Kapkupi/RPI5-Palmtop/CAD/SolidWorks/heatsink/raspberry-pi-5-2.snapshot.8/Photo/iWcUdrz5w2npCPwYrjM4Qg-970-80.jpg

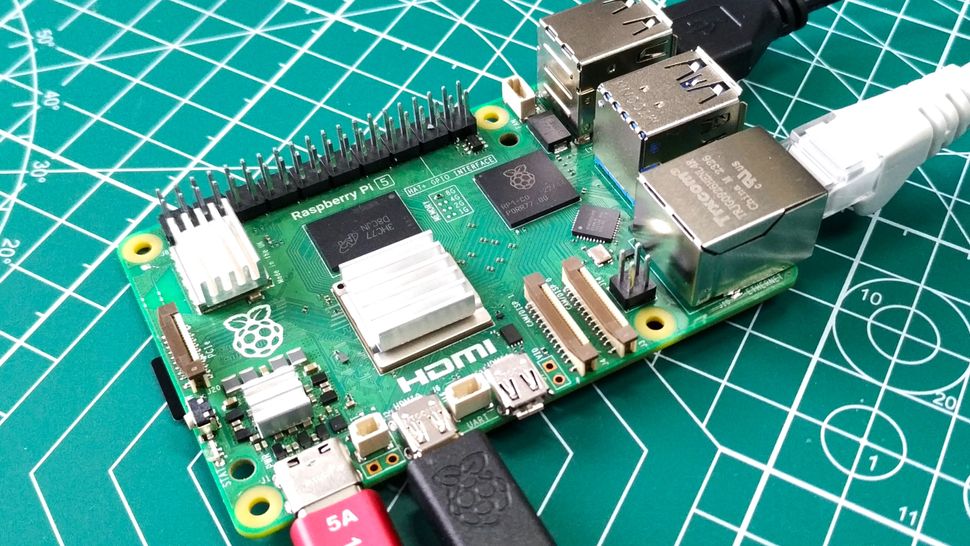
CAD/SolidWorks/heatsink/raspberry-pi-5-2.snapshot.8/Photo/iWcUdrz5w2npCPwYrjM4Qg-970-80.jpg
