Kapkupi/RPI5-Palmtop/CAD/SolidWorks/heatsink/raspberry-pi-5-2.snapshot.8/Photo/raspberry pi 5.png

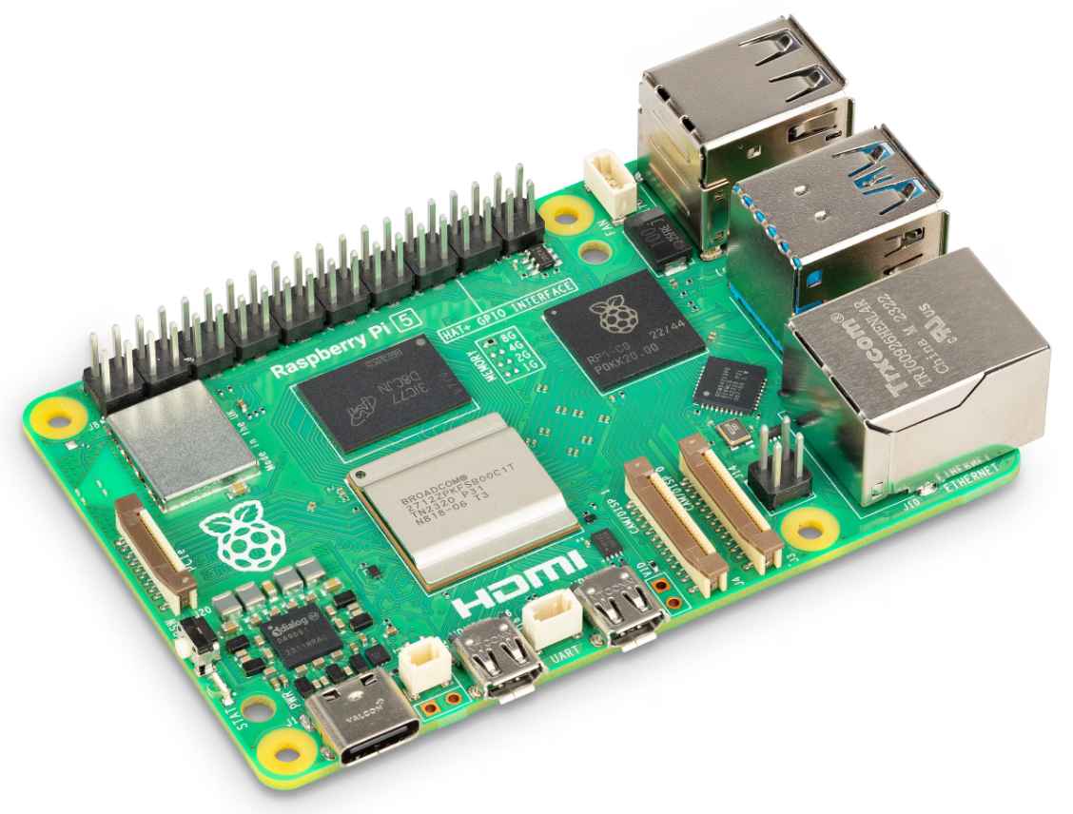
CAD/SolidWorks/heatsink/raspberry-pi-5-2.snapshot.8/Photo/raspberry pi 5.png
