Kapkupi/RPI5-Palmtop/CAD/SolidWorks/heatsink/raspberry-pi-5-2.snapshot.8/RENDERS/Raspberry Pi (2)_Ładny wygląd.png

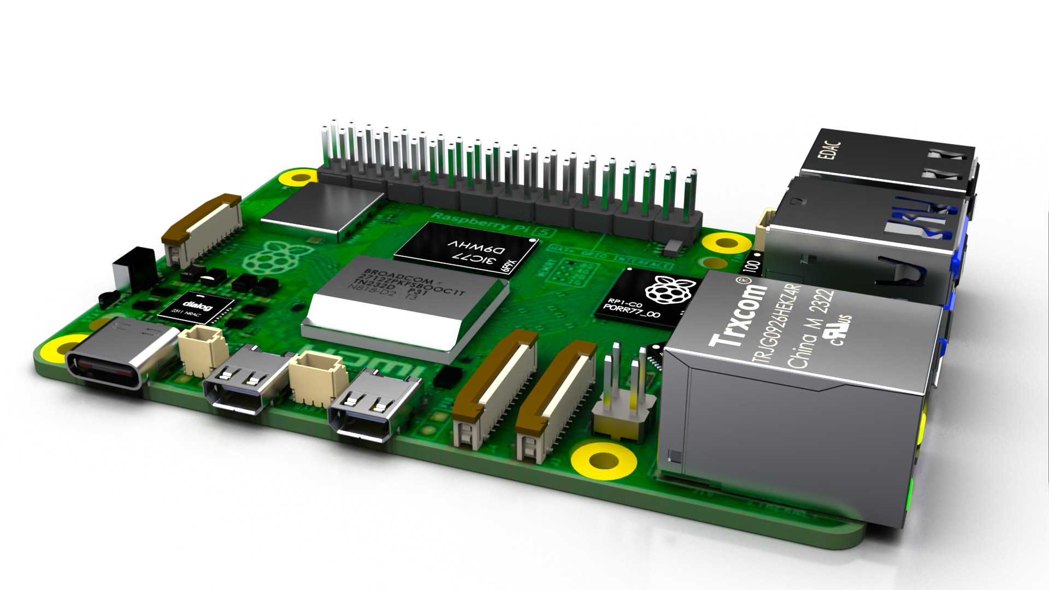
CAD/SolidWorks/heatsink/raspberry-pi-5-2.snapshot.8/RENDERS/Raspberry Pi (2)_Ładny wygląd.png
