Kapkupi/RPI5-Palmtop/CAD/SolidWorks/heatsink/raspberry-pi-5-2.snapshot.8/RENDERS/RASPBERRY_PI_5_1.png

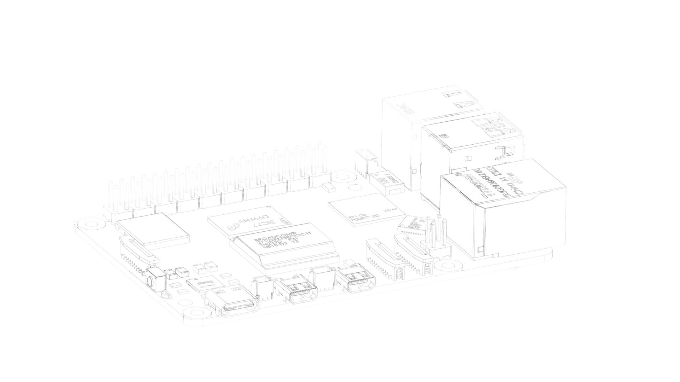
CAD/SolidWorks/heatsink/raspberry-pi-5-2.snapshot.8/RENDERS/RASPBERRY_PI_5_1.png
