Kapkupi/RPI5-Palmtop/step/face_plate.STEP

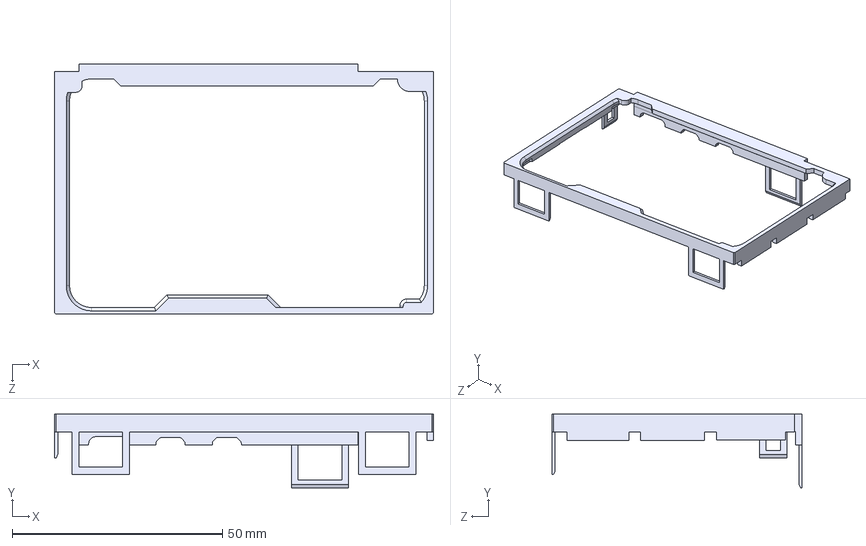
[picture p26: CAD file, 2026-09-20]
step/face_plate.STEP
90.2 x 17.5 x 59.6 mm
