Kapkupi/RPI5-Palmtop/CAD/SolidWorks/heatsink/display_button.SLDPRT

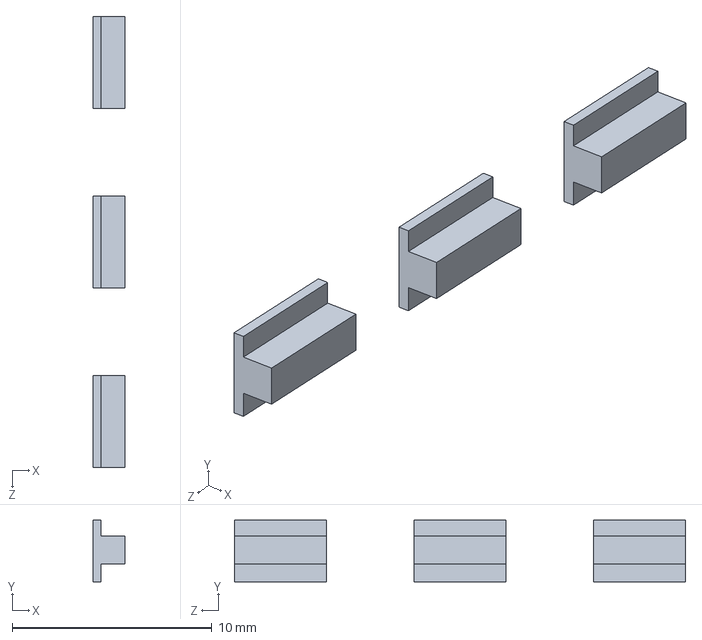
[picture p27: CAD file, 2026-09-20]
CAD/SolidWorks/heatsink/display_button.SLDPRT
1.60 x 3.10 x 22.6 mm
