Kapkupi/RPI5-Palmtop/CAD/SolidWorks/heatsink/raspberry-pi-5-2.snapshot.8/PARTS/DISPLAY_CONNECTOR/1.1 part 1 metal pin.SLDPRT

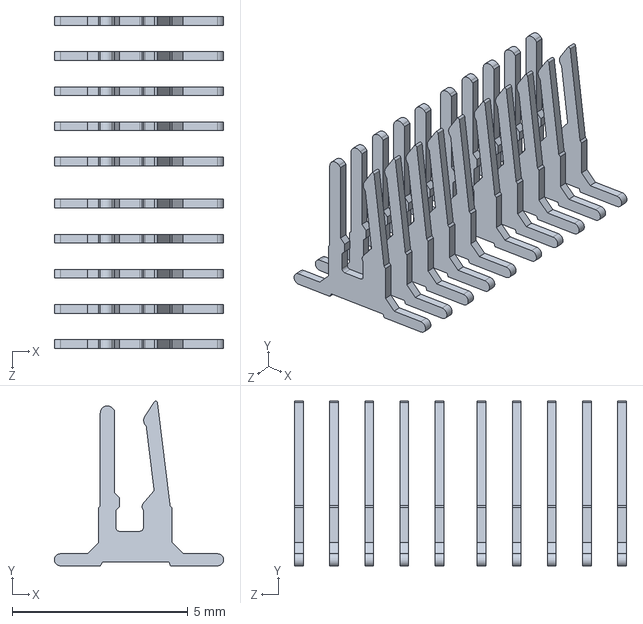
[picture p28: CAD file, 2026-08-03]
CAD/SolidWorks/heatsink/raspberry-pi-5-2.snapshot.8/PARTS/DISPLAY_CONNECTOR/1.1 part 1 metal pin.SLDPRT
4.82 x 4.69 x 9.45 mm
