Kapkupi/RPI5-Palmtop/CAD/SolidWorks/heatsink/raspberry-pi-5-2.snapshot.8/PARTS/STOCK_2.SLDPRT

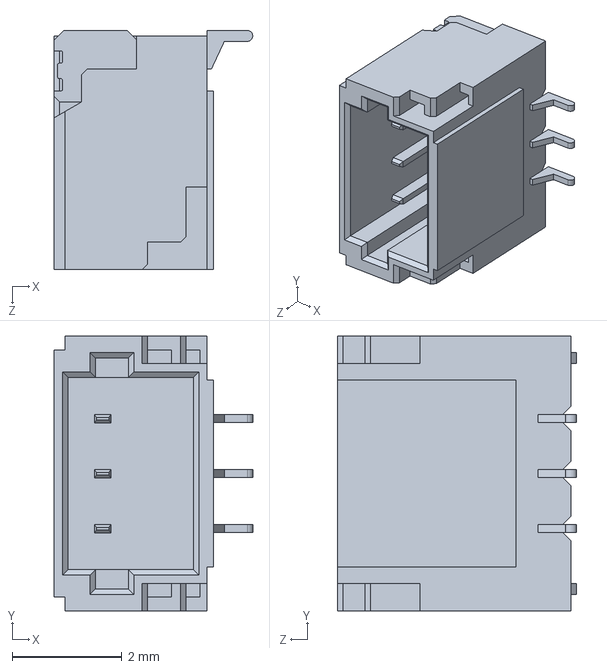
[picture p29: CAD file, 2026-08-03]
CAD/SolidWorks/heatsink/raspberry-pi-5-2.snapshot.8/PARTS/STOCK_2.SLDPRT
3.61 x 5.00 x 4.35 mm
