Kapkupi/RPI5-Palmtop/CAD/SolidWorks/open/raspberry-pi-5-2.snapshot.8/PARTS/3.0_PIN_HEADER_10.SLDPRT

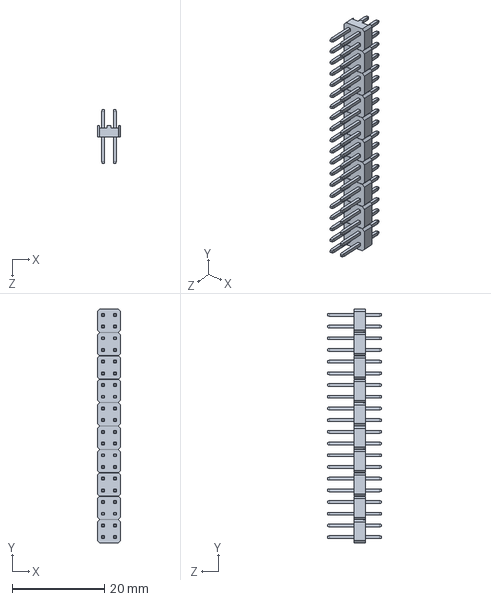
[picture p30: CAD file, 2026-08-03]
CAD/SolidWorks/open/raspberry-pi-5-2.snapshot.8/PARTS/3.0_PIN_HEADER_10.SLDPRT
5.08 x 50.8 x 11.8 mm
