Kapkupi/RPI5-Palmtop/CAD/SolidWorks/open/raspberry-pi-5-2.snapshot.8/PARTS/DISPLAY_CONNECTOR/2.2 part 2 with combine.SLDPRT

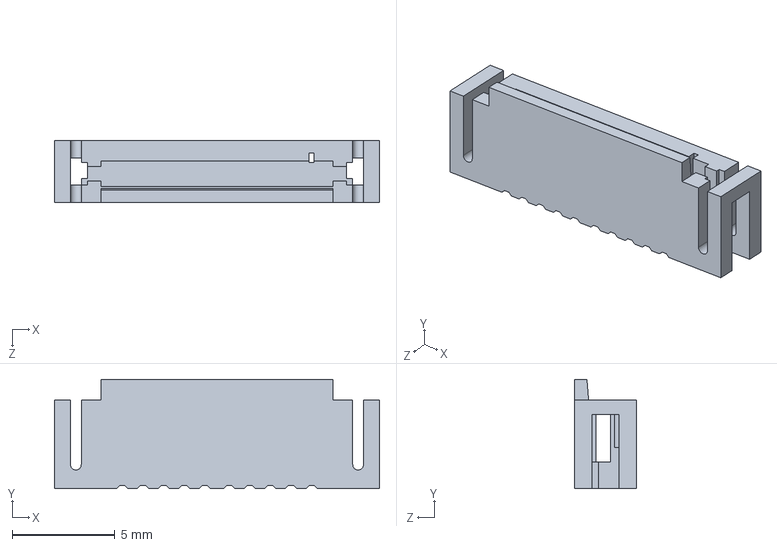
[picture p31: CAD file, 2026-08-03]
CAD/SolidWorks/open/raspberry-pi-5-2.snapshot.8/PARTS/DISPLAY_CONNECTOR/2.2 part 2 with combine.SLDPRT
15.8 x 5.30 x 3.00 mm
