Kapkupi/RPI5-Palmtop/CAD/SolidWorks/heatsink/raspberry-pi-5-2.snapshot.8/PARTS/2xUSB_3.0_PORT.SLDPRT

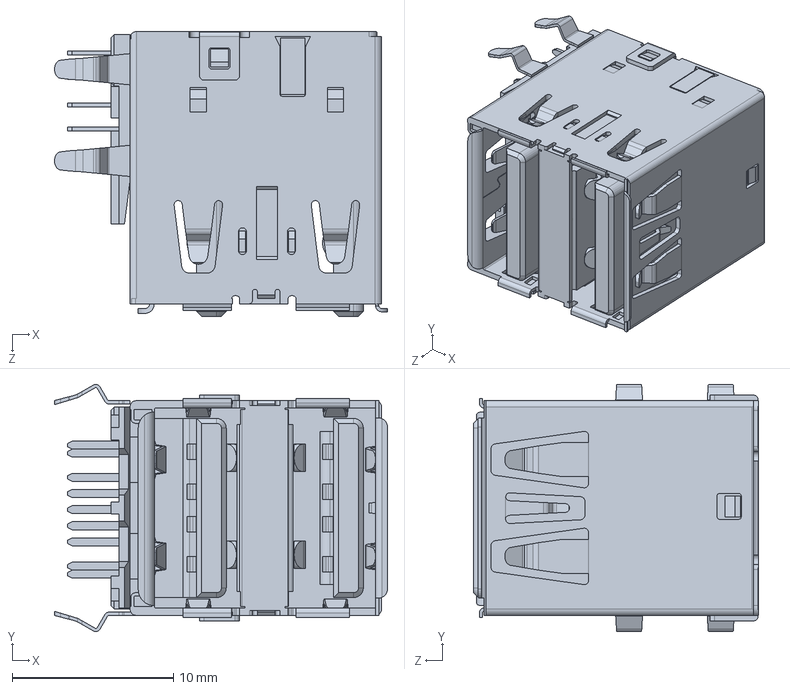
[picture p32: CAD file, 2026-08-03]
CAD/SolidWorks/heatsink/raspberry-pi-5-2.snapshot.8/PARTS/2xUSB_3.0_PORT.SLDPRT
20.6 x 15.3 x 17.7 mm
