Kapkupi/RPI5-Palmtop/CAD/SolidWorks/heatsink/raspberry-pi-5-2.snapshot.8/PARTS/SD CARD/PART3_V1.SLDPRT

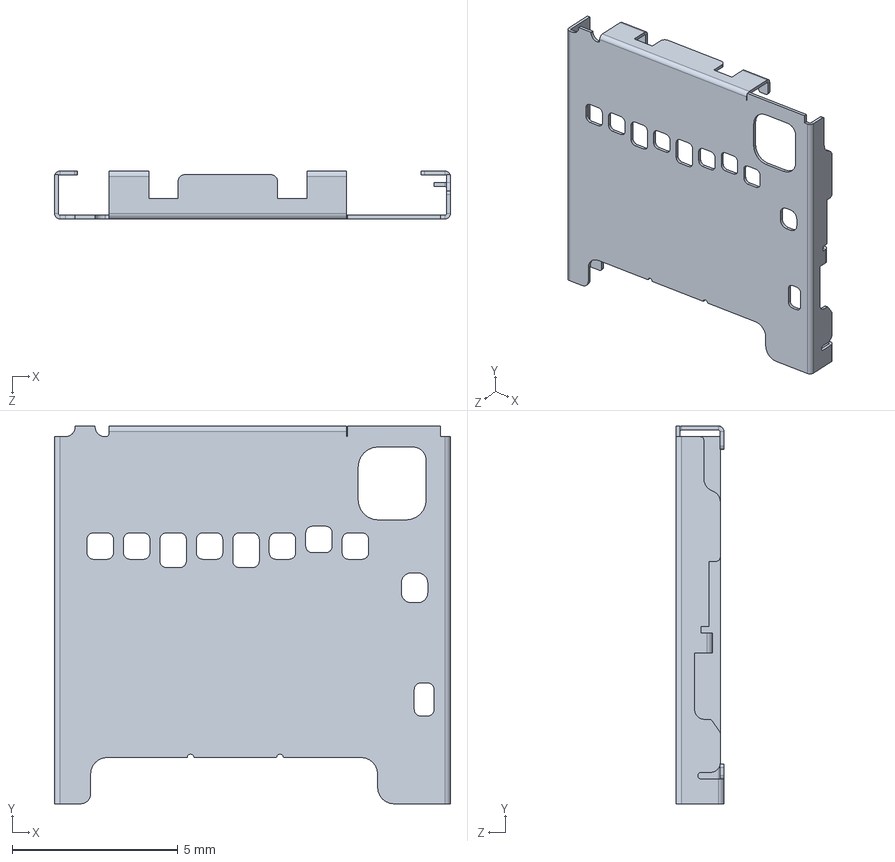
[picture p33: CAD file, 2026-08-03]
CAD/SolidWorks/heatsink/raspberry-pi-5-2.snapshot.8/PARTS/SD CARD/PART3_V1.SLDPRT
11.9 x 11.4 x 1.45 mm
