Kapkupi/RPI5-Palmtop/CAD/SolidWorks/open/power_button.SLDPRT

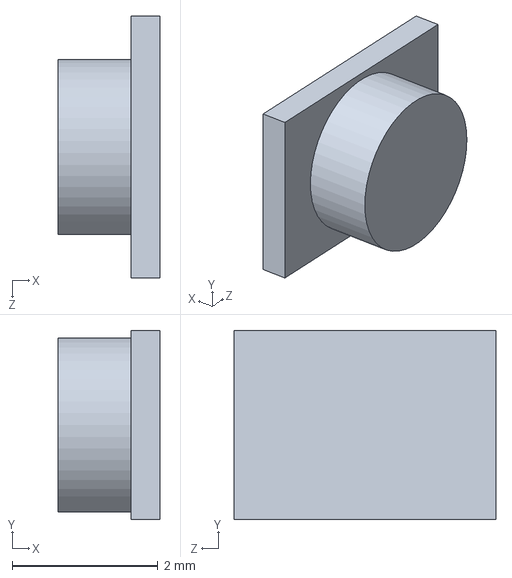
[picture p34: CAD file, 2026-09-20]
CAD/SolidWorks/open/power_button.SLDPRT
1.40 x 2.60 x 3.60 mm
