Kapkupi/RPI5-Palmtop/CAD/SolidWorks/open/raspberry-pi-5-2.snapshot.8/PARTS/MxL.SLDPRT

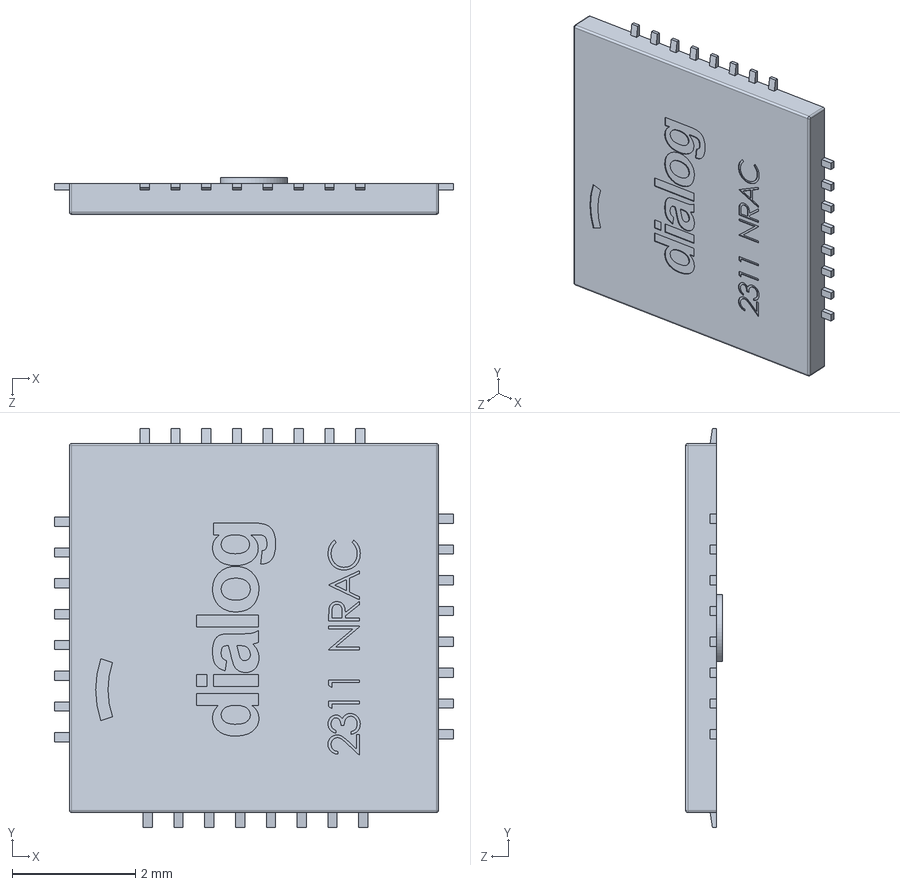
[picture p35: CAD file, 2026-08-03]
CAD/SolidWorks/open/raspberry-pi-5-2.snapshot.8/PARTS/MxL.SLDPRT
6.48 x 6.48 x 0.6 mm
