Kapkupi/RPI5-Palmtop/step/display_case.STEP

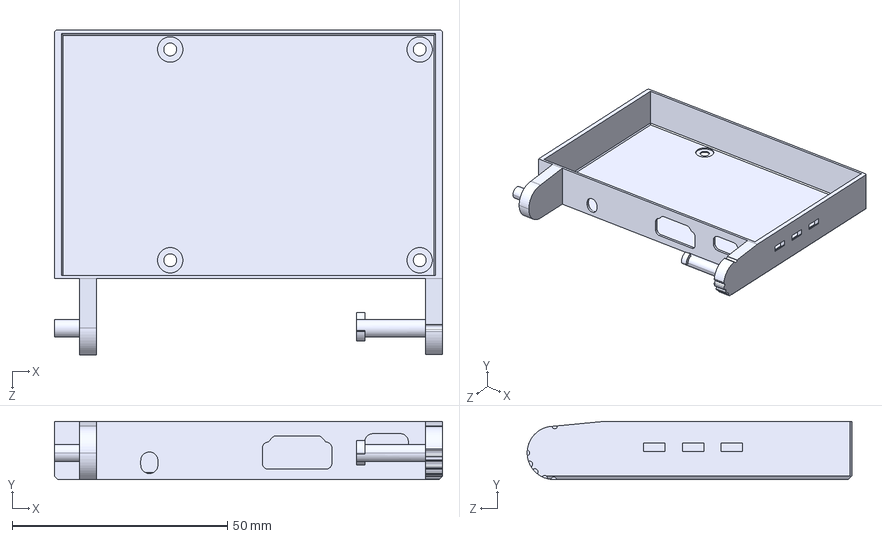
[picture p36: CAD file, 2026-09-20]
step/display_case.STEP
90.2 x 13.5 x 75.5 mm
