Kapkupi/RPI5-Palmtop/CAD/SolidWorks/open/spring.SLDPRT

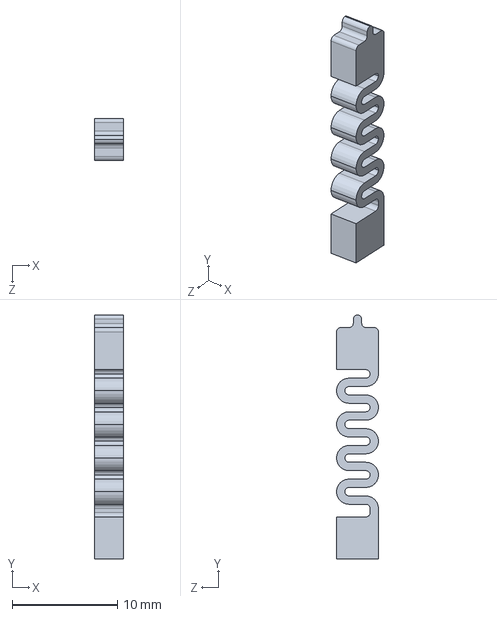
[picture p38: CAD file, 2026-09-20]
CAD/SolidWorks/open/spring.SLDPRT
2.80 x 23.2 x 4.00 mm
