Kapkupi/RPI5-Palmtop/step/display_button.STEP

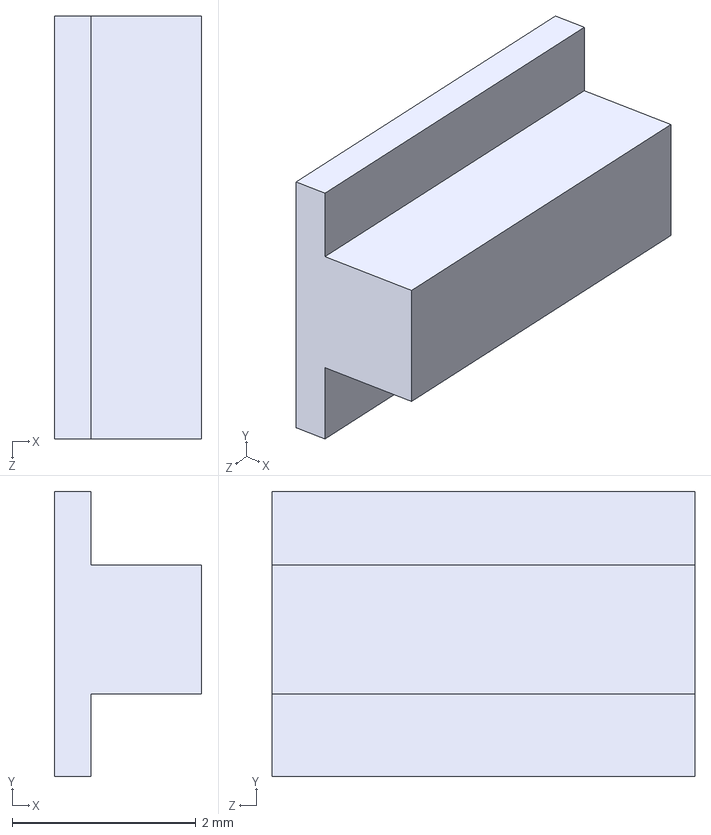
[picture p39: CAD file, 2026-09-20]
step/display_button.STEP
1.60 x 3.10 x 4.60 mm
