Kapkupi/RPI5-Palmtop/CAD/SolidWorks/open/raspberry-pi-5-2.snapshot.8/PARTS/STOCK_1.SLDPRT

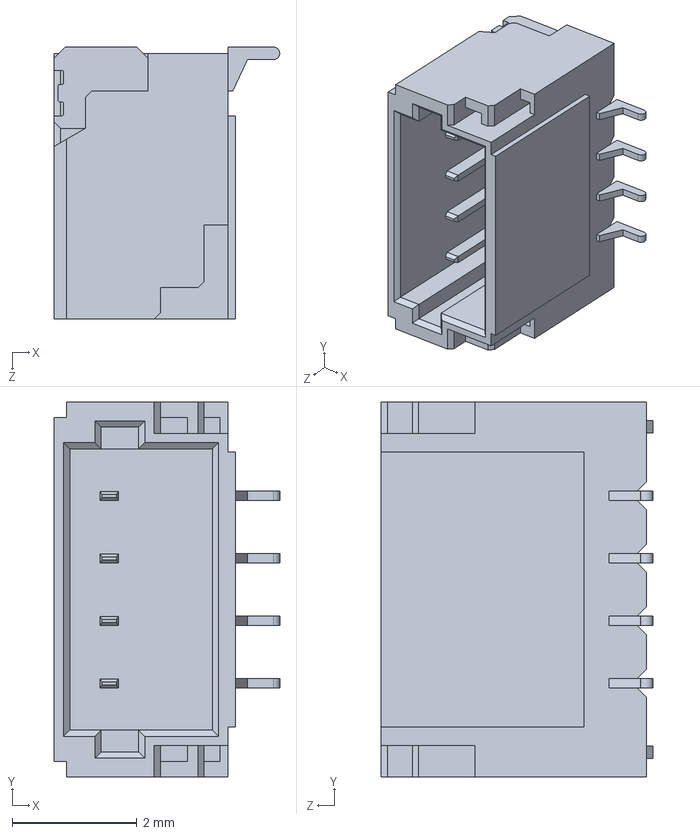
[picture p41: CAD file, 2026-08-03]
CAD/SolidWorks/open/raspberry-pi-5-2.snapshot.8/PARTS/STOCK_1.SLDPRT
3.61 x 6.00 x 4.35 mm
