Kapkupi/RPI5-Palmtop/CAD/SolidWorks/heatsink/raspberry-pi-5-2.snapshot.8/PARTS/BUTTON_MINI.SLDPRT

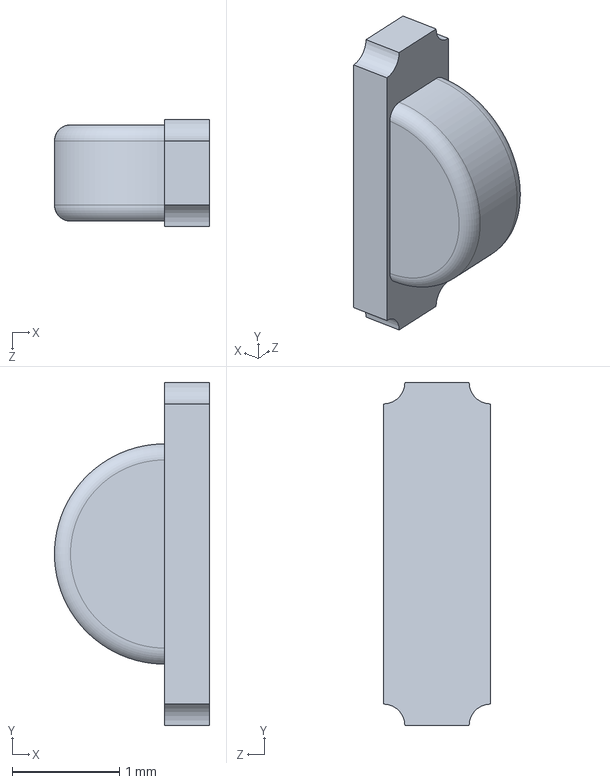
[picture p42: CAD file, 2026-08-03]
CAD/SolidWorks/heatsink/raspberry-pi-5-2.snapshot.8/PARTS/BUTTON_MINI.SLDPRT
1.45 x 3.20 x 1 mm
