Kapkupi/RPI5-Palmtop/CAD/SolidWorks/open/raspberry-pi-5-2.snapshot.8/PARTS/BROADCOM_1.SLDPRT

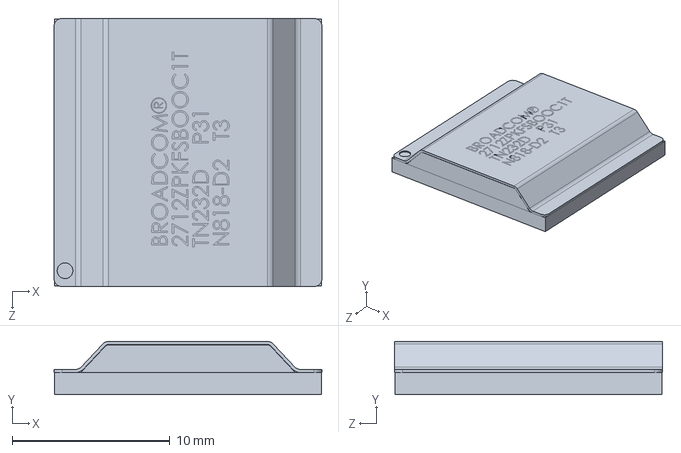
[picture p43: CAD file, 2026-08-03]
CAD/SolidWorks/open/raspberry-pi-5-2.snapshot.8/PARTS/BROADCOM_1.SLDPRT
17.0 x 3.38 x 17.0 mm
