Kapkupi/RPI5-Palmtop/CAD/SolidWorks/heatsink/raspberry-pi-5-2.snapshot.8/PARTS/FEMALE_USB_CONNECTOR.SLDPRT

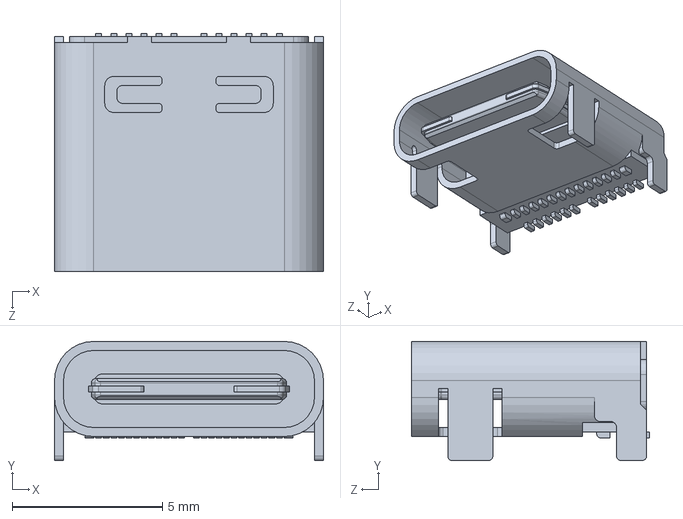
[picture p44: CAD file, 2026-08-03]
CAD/SolidWorks/heatsink/raspberry-pi-5-2.snapshot.8/PARTS/FEMALE_USB_CONNECTOR.SLDPRT
8.94 x 3.96 x 7.90 mm
