Kapkupi/RPI5-Palmtop/CAD/SolidWorks/heatsink/raspberry-pi-5-2.snapshot.8/PARTS/FEMALE_MICRO_HDMI_CONNECTOR.SLDPRT

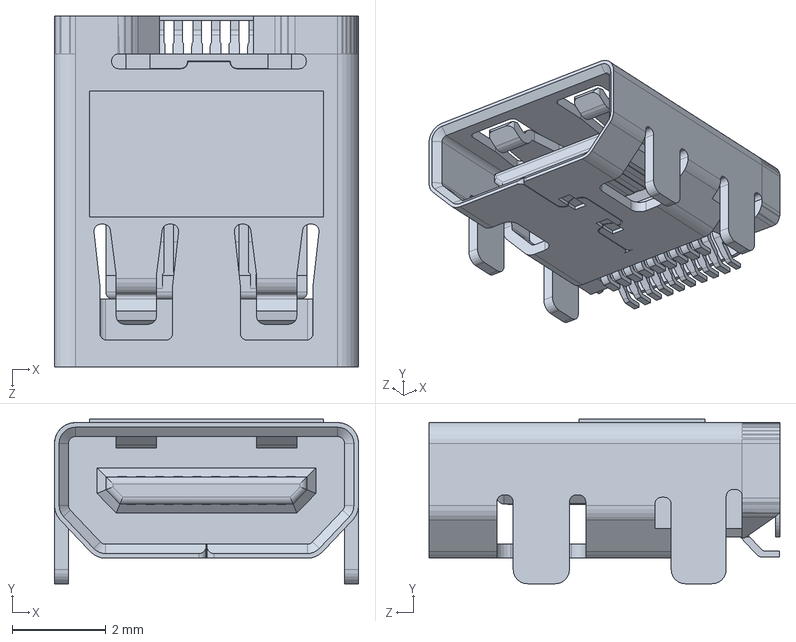
[picture p45: CAD file, 2026-08-03]
CAD/SolidWorks/heatsink/raspberry-pi-5-2.snapshot.8/PARTS/FEMALE_MICRO_HDMI_CONNECTOR.SLDPRT
6.50 x 3.52 x 7.50 mm
