Kapkupi/RPI5-Palmtop/CAD/SolidWorks/open/raspberry-pi-5-2.snapshot.8/PARTS/2xUSB_2.0_PORT.SLDPRT

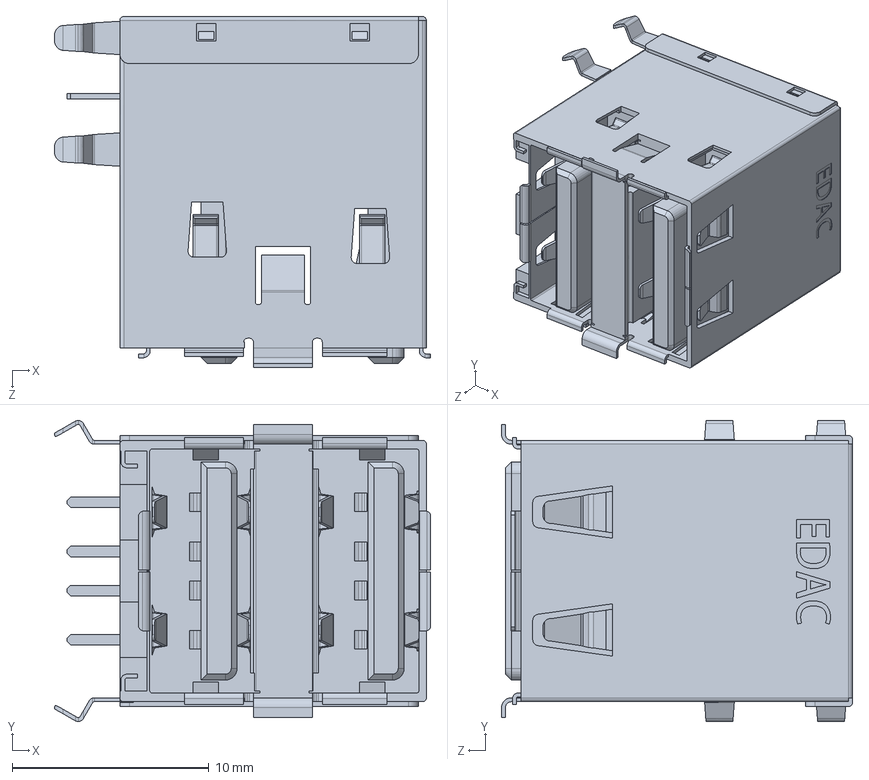
[picture p46: CAD file, 2026-08-03]
CAD/SolidWorks/open/raspberry-pi-5-2.snapshot.8/PARTS/2xUSB_2.0_PORT.SLDPRT
19.2 x 15.3 x 17.9 mm
