Kapkupi/RPI5-Palmtop/CAD/SolidWorks/heatsink/raspberry-pi-5-2.snapshot.8/PARTS/CONNECT_V1.SLDPRT

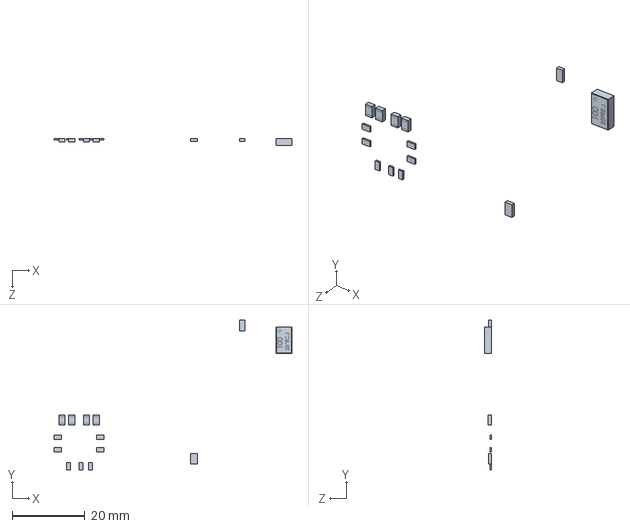
[picture p47: CAD file, 2026-08-03]
CAD/SolidWorks/heatsink/raspberry-pi-5-2.snapshot.8/PARTS/CONNECT_V1.SLDPRT
65.4 x 41.1 x 2.00 mm
