Kapkupi/RPI5-Palmtop/CAD/SolidWorks/open/raspberry-pi-5-2.snapshot.8/PARTS/CAMERA_DISPLAY_2.SLDPRT

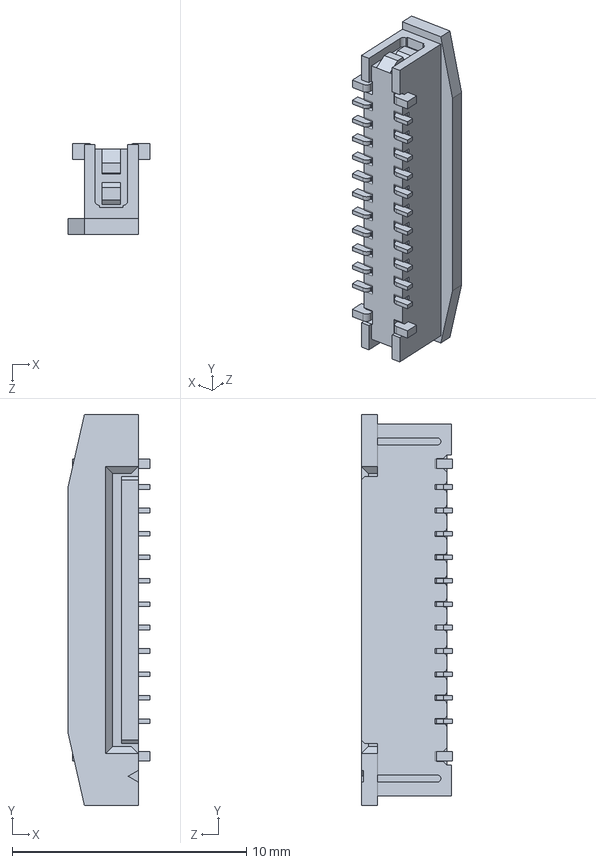
[picture p48: CAD file, 2026-08-03]
CAD/SolidWorks/open/raspberry-pi-5-2.snapshot.8/PARTS/CAMERA_DISPLAY_2.SLDPRT
3.50 x 16.7 x 3.90 mm
