Kapkupi/RPI5-Palmtop/CAD/SolidWorks/heatsink/raspberry-pi-5-2.snapshot.8/PARTS/GIGABIT_ETHERNET_PORT.SLDPRT

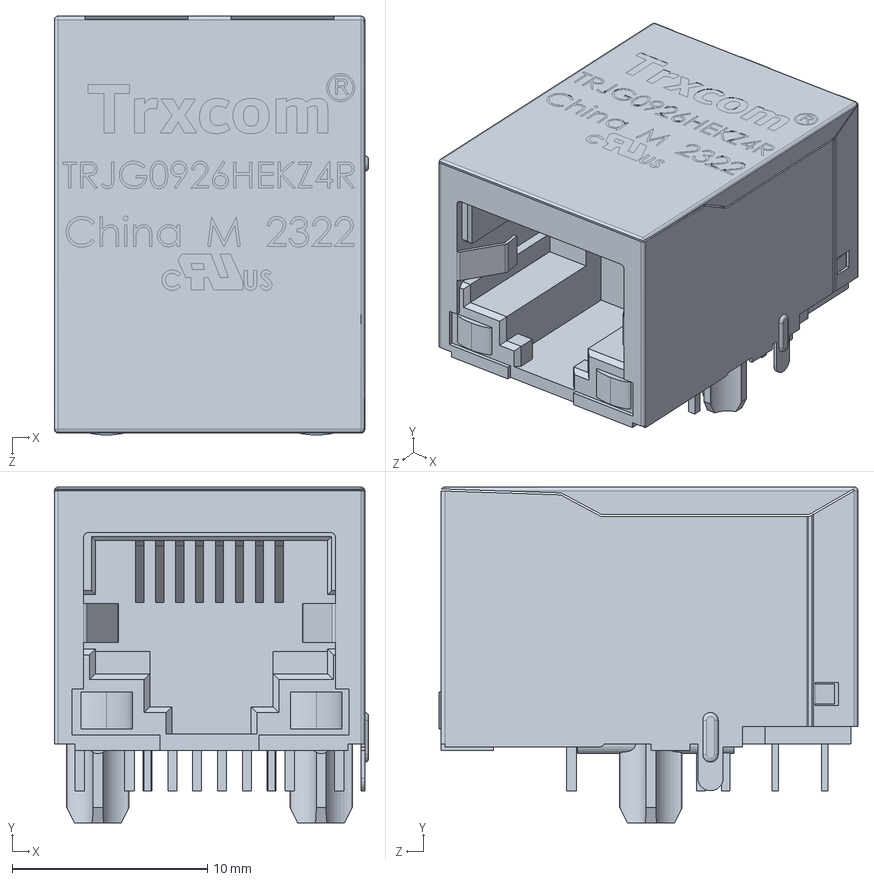
[picture p49: CAD file, 2026-08-03]
CAD/SolidWorks/heatsink/raspberry-pi-5-2.snapshot.8/PARTS/GIGABIT_ETHERNET_PORT.SLDPRT
16.1 x 17.2 x 21.4 mm
