Kapkupi/RPI5-Palmtop/CAD/SolidWorks/heatsink/raspberry-pi-5-2.snapshot.8/PARTS/PLATE_RASPBERRY_PI_5.SLDPRT

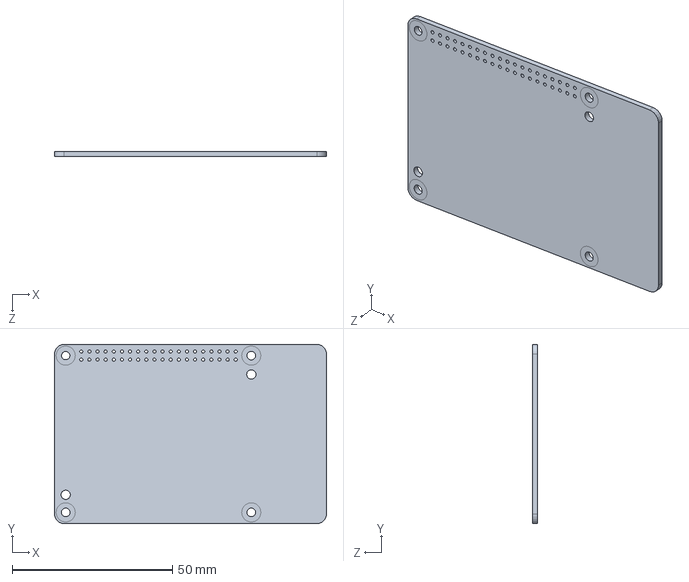
[picture p50: CAD file, 2026-08-03]
CAD/SolidWorks/heatsink/raspberry-pi-5-2.snapshot.8/PARTS/PLATE_RASPBERRY_PI_5.SLDPRT
85.0 x 56.0 x 1.70 mm
