Kapkupi/RPI5-Palmtop/CAD/SolidWorks/open/raspberry-pi-5-2.snapshot.8/PARTS/BUTTON_2.SLDPRT

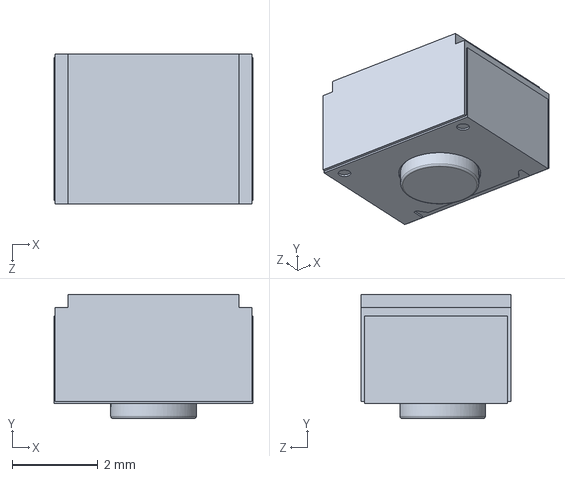
[picture p51: CAD file, 2026-08-03]
CAD/SolidWorks/open/raspberry-pi-5-2.snapshot.8/PARTS/BUTTON_2.SLDPRT
4.65 x 2.90 x 3.50 mm
