Kapkupi/RPI5-Palmtop/CAD/SolidWorks/heatsink/raspberry-pi-5-2.snapshot.8/PARTS/METAL_PLATE..SLDPRT

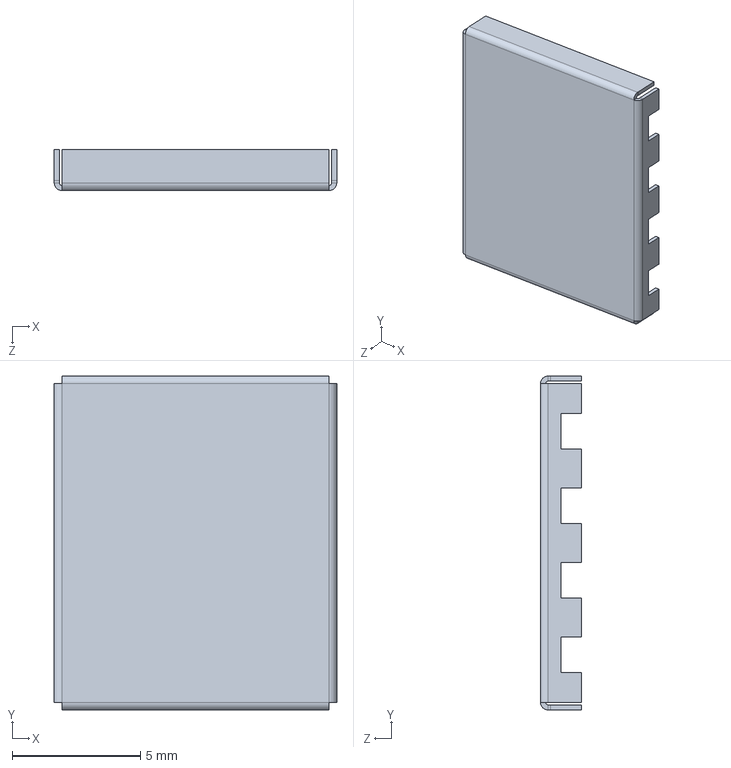
[picture p52: CAD file, 2026-08-03]
CAD/SolidWorks/heatsink/raspberry-pi-5-2.snapshot.8/PARTS/METAL_PLATE..SLDPRT
11.0 x 13.0 x 1.60 mm
