Kapkupi/RPI5-Palmtop/CAD/SolidWorks/heatsink/raspberry-pi-5-2.snapshot.8/PARTS/RP1_CO_CONTROLLER.SLDPRT

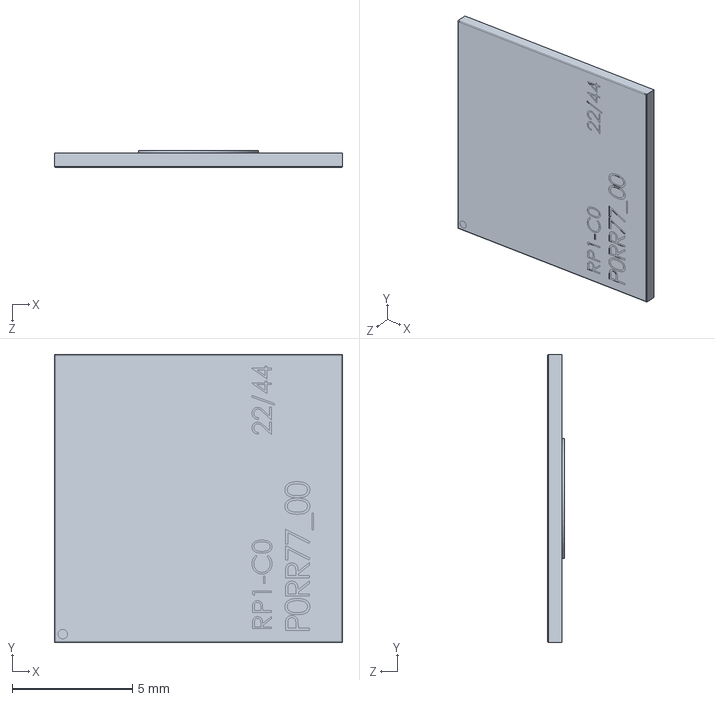
[picture p53: CAD file, 2026-08-03]
CAD/SolidWorks/heatsink/raspberry-pi-5-2.snapshot.8/PARTS/RP1_CO_CONTROLLER.SLDPRT
12.0 x 12.0 x 0.7 mm
