Kapkupi/RPI5-Palmtop/CAD/SolidWorks/open/raspberry-pi-5-2.snapshot.8/PARTS/GIGABIT_ETHERNET_TRANSCEIVER.SLDPRT

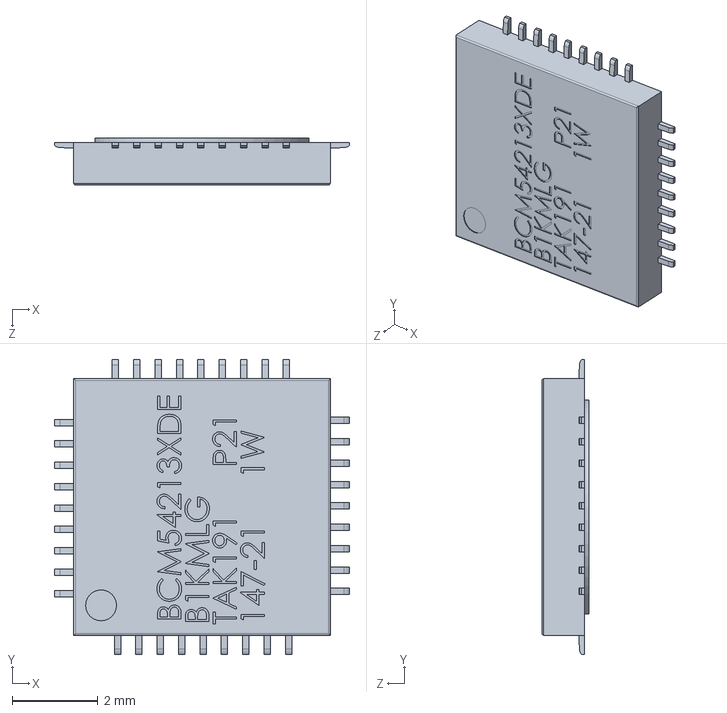
[picture p54: CAD file, 2026-08-03]
CAD/SolidWorks/open/raspberry-pi-5-2.snapshot.8/PARTS/GIGABIT_ETHERNET_TRANSCEIVER.SLDPRT
6.90 x 6.90 x 1.10 mm
